danwerner21/6502PC/images/1000006746.jpg

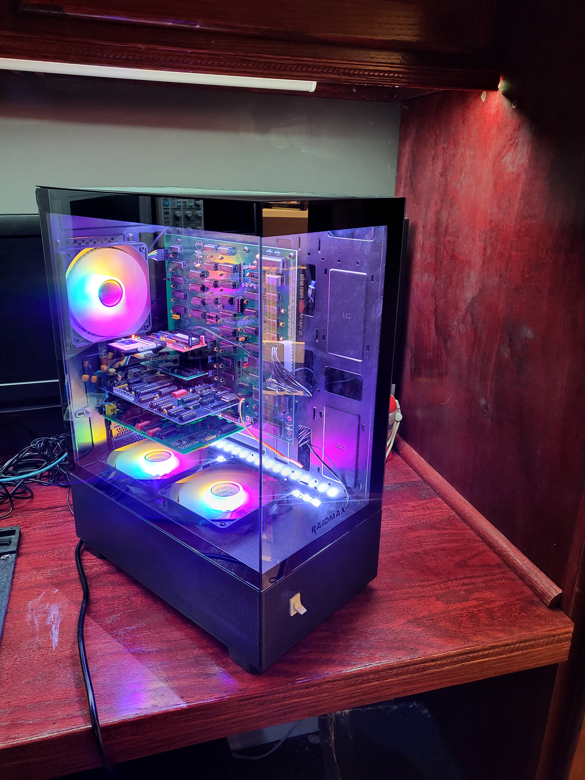
images/1000006746.jpg
